EthanL67/teensy-dsp/case/PLH-8 LED holder.SLDASM

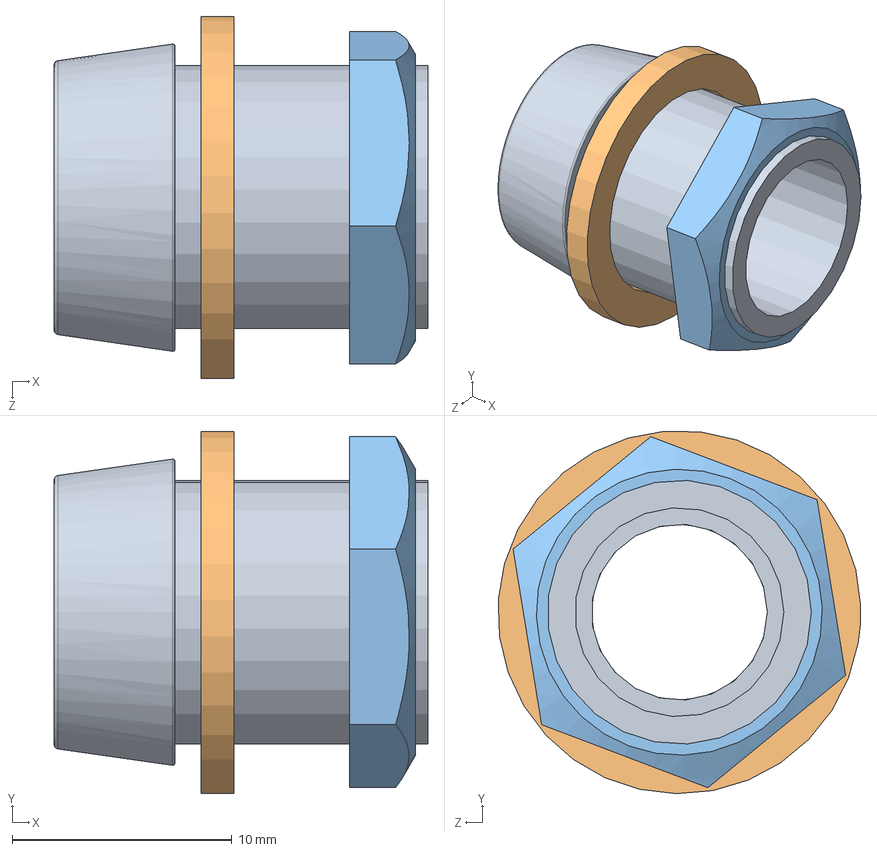
[picture p8: CAD file, 2023-11-12]
case/PLH-8 LED holder.SLDASM
17.0 x 16.5 x 16.5 mm
PLH-8 LED holder - body
PLH-8 LED holder - spacer
PLH-8 LED holder - nut
