EthanL67/teensy-dsp/case/case-lid.SLDPRT

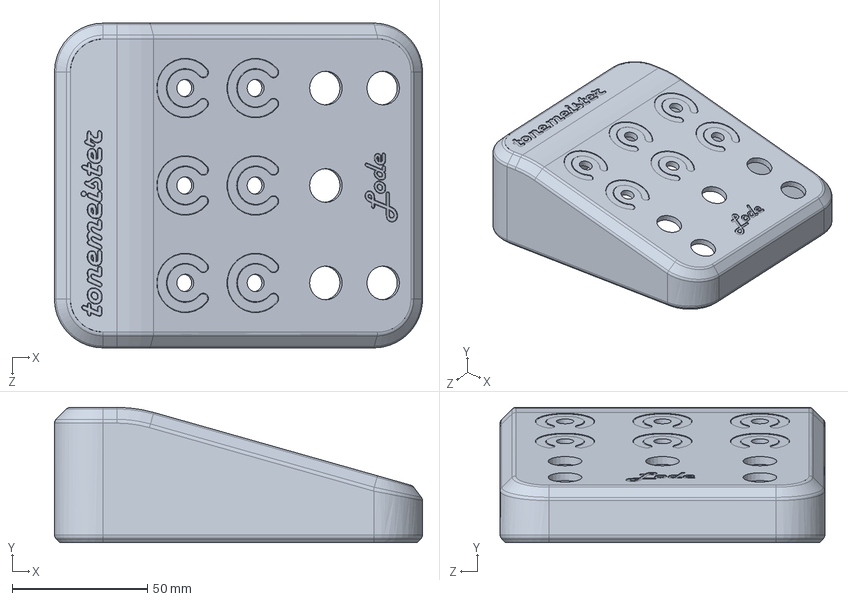
[picture p9: CAD file, 2023-11-18]
case/case-lid.SLDPRT
136.0 x 50.0 x 120.0 mm
