EthanL67/teensy-dsp/case/nameplate-inlay.SLDPRT

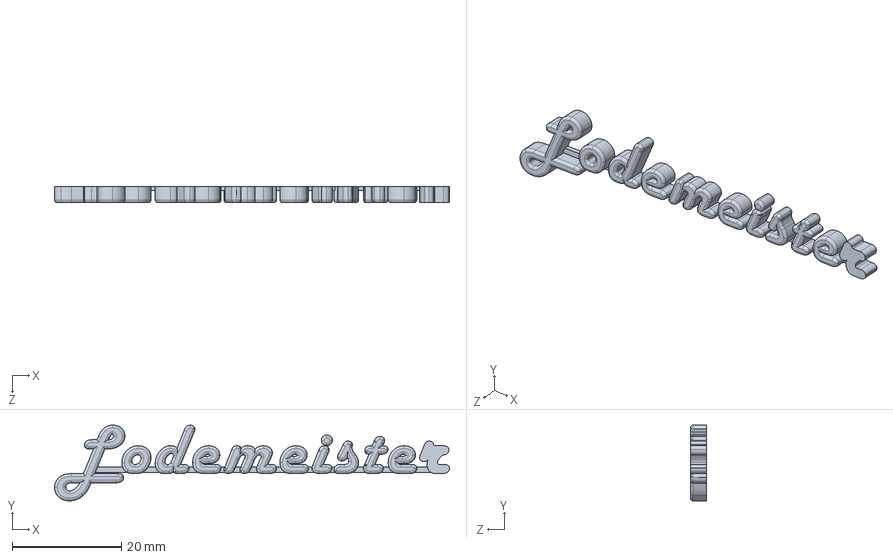
[picture p10: CAD file, 2023-11-13]
case/nameplate-inlay.SLDPRT
72.2 x 13.9 x 3.00 mm
