EthanL67/teensy-dsp/case/knob-inlay.SLDPRT

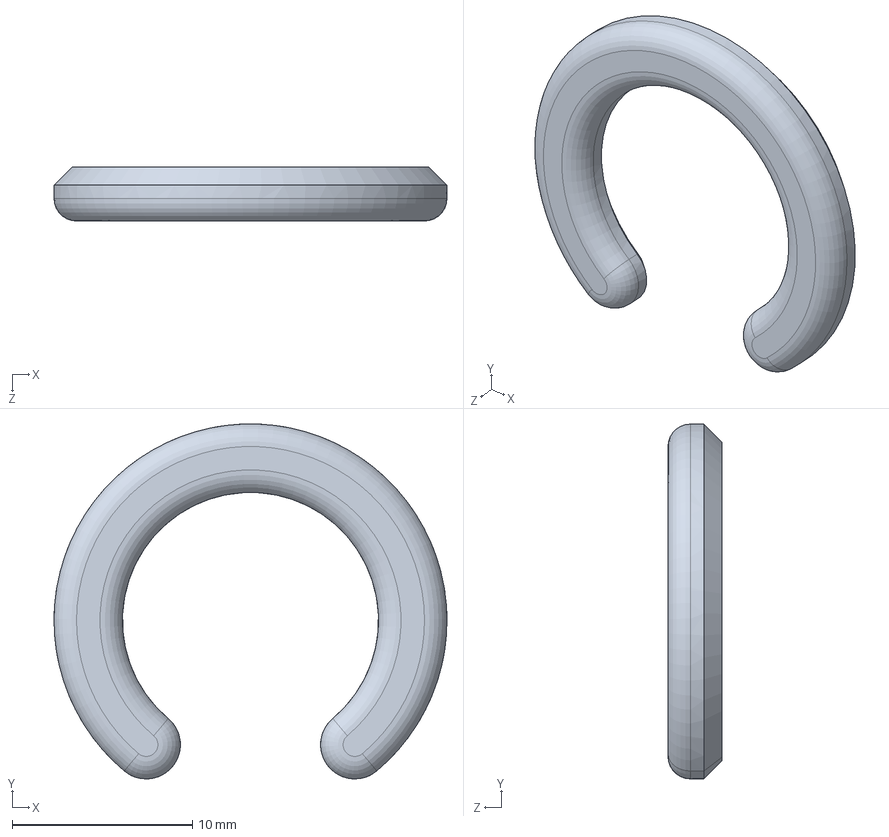
[picture p11: CAD file, 2023-11-12]
case/knob-inlay.SLDPRT
21.8 x 19.7 x 3.00 mm
