EthanL67/teensy-dsp/case/57GB5FX--3DModel-STEP-1.SLDPRT

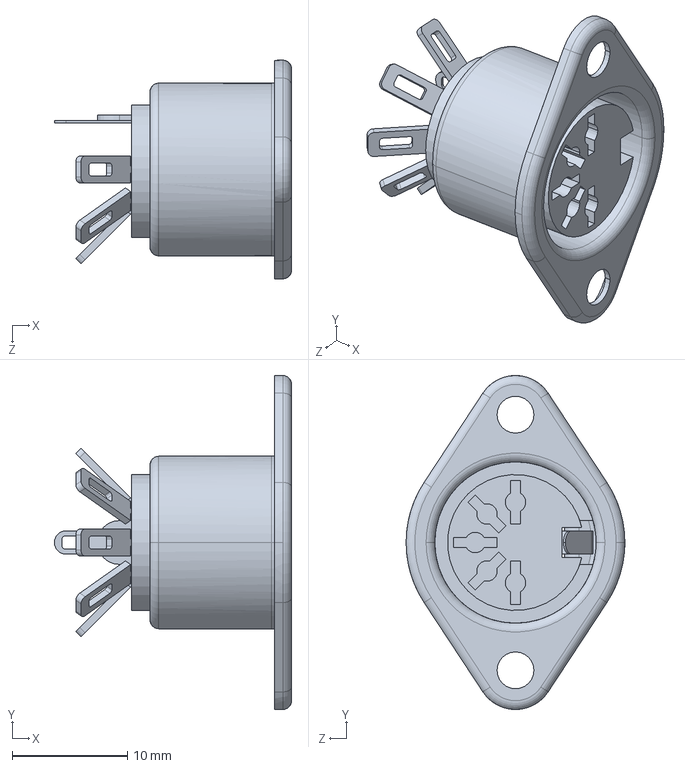
[picture p12: CAD file, 2023-11-12]
case/57GB5FX--3DModel-STEP-1.SLDPRT
20.6 x 29.0 x 19.0 mm
