EthanL67/teensy-dsp/case/LED-8mm.SLDPRT

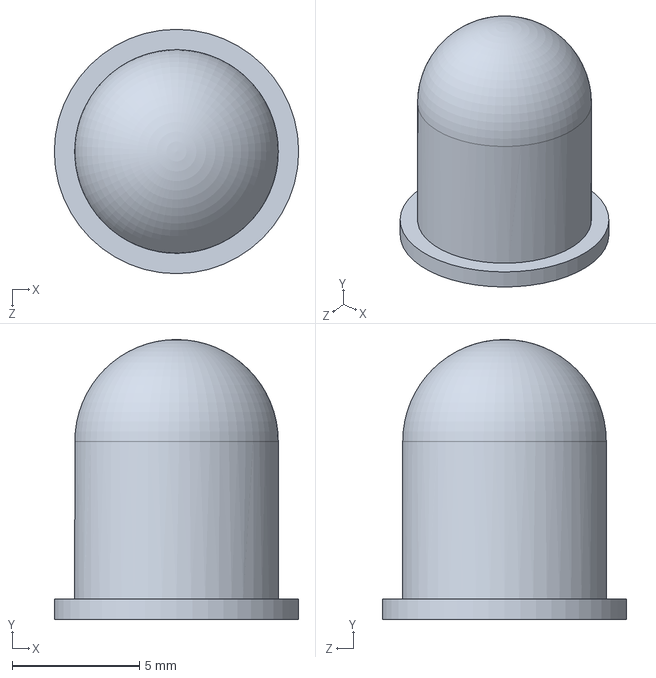
[picture p13: CAD file, 2023-11-12]
case/LED-8mm.SLDPRT
9.60 x 11.0 x 9.60 mm
